46cv8/HoloBlade/electronics/Flex_V1/flex_v1.sch

## EAGLE design electronics/Flex_V1/flex_v1.sch (2020-11-19)

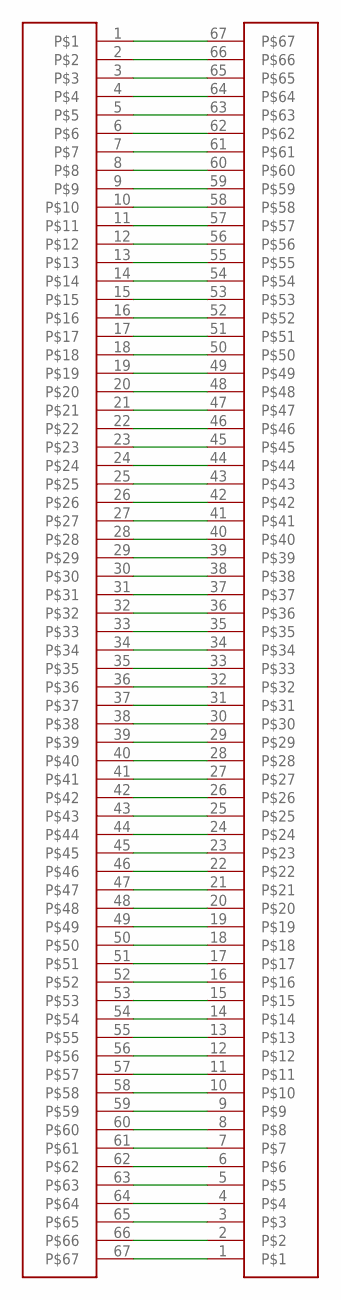
[picture p3: schematic flex_v1.sch]

Parts:
U$1: CONN_FFC_67WAY; CONN_67WAY_FFC_LCD
U$2: CONN_FFC_67WAY_PCB; CONN_67WAY_FFC_PCB

Connections:
unnamed: U$1.67, U$2.1
unnamed: U$1.66, U$2.2
unnamed: U$1.65, U$2.3
unnamed: U$1.64, U$2.4
unnamed: U$1.63, U$2.5
unnamed: U$1.62, U$2.6
unnamed: U$1.61, U$2.7
unnamed: U$1.60, U$2.8
unnamed: U$1.59, U$2.9
unnamed: U$1.58, U$2.10
unnamed: U$1.57, U$2.11
unnamed: U$1.56, U$2.12
unnamed: U$1.55, U$2.13
unnamed: U$1.54, U$2.14
unnamed: U$1.53, U$2.15
unnamed: U$1.52, U$2.16
unnamed: U$1.51, U$2.17
unnamed: U$1.50, U$2.18
unnamed: U$1.49, U$2.19
unnamed: U$1.48, U$2.20
unnamed: U$1.47, U$2.21
unnamed: U$1.46, U$2.22
unnamed: U$1.45, U$2.23
unnamed: U$1.44, U$2.24
unnamed: U$1.43, U$2.25
unnamed: U$1.42, U$2.26
unnamed: U$1.41, U$2.27
unnamed: U$1.40, U$2.28
unnamed: U$1.39, U$2.29
unnamed: U$1.38, U$2.30
unnamed: U$1.37, U$2.31
unnamed: U$1.36, U$2.32
unnamed: U$1.35, U$2.33
unnamed: U$1.34, U$2.34
unnamed: U$1.33, U$2.35
unnamed: U$1.32, U$2.36
unnamed: U$1.31, U$2.37
unnamed: U$1.30, U$2.38
unnamed: U$1.29, U$2.39
unnamed: U$1.28, U$2.40
unnamed: U$1.27, U$2.41
unnamed: U$1.26, U$2.42
unnamed: U$1.25, U$2.43
unnamed: U$1.24, U$2.44
unnamed: U$1.23, U$2.45
unnamed: U$1.22, U$2.46
unnamed: U$1.21, U$2.47
unnamed: U$1.20, U$2.48
unnamed: U$1.19, U$2.49
unnamed: U$1.18, U$2.50
unnamed: U$1.17, U$2.51
unnamed: U$1.16, U$2.52
unnamed: U$1.15, U$2.53
unnamed: U$1.14, U$2.54
unnamed: U$1.13, U$2.55
unnamed: U$1.12, U$2.56
unnamed: U$1.11, U$2.57
unnamed: U$1.10, U$2.58
unnamed: U$1.9, U$2.59
unnamed: U$1.8, U$2.60
unnamed: U$1.7, U$2.61
unnamed: U$1.6, U$2.62
unnamed: U$1.5, U$2.63
unnamed: U$1.4, U$2.64
unnamed: U$1.3, U$2.65
unnamed: U$1.2, U$2.66
unnamed: U$1.1, U$2.67
